visrealm/pico9918/img/digital_av.jpg

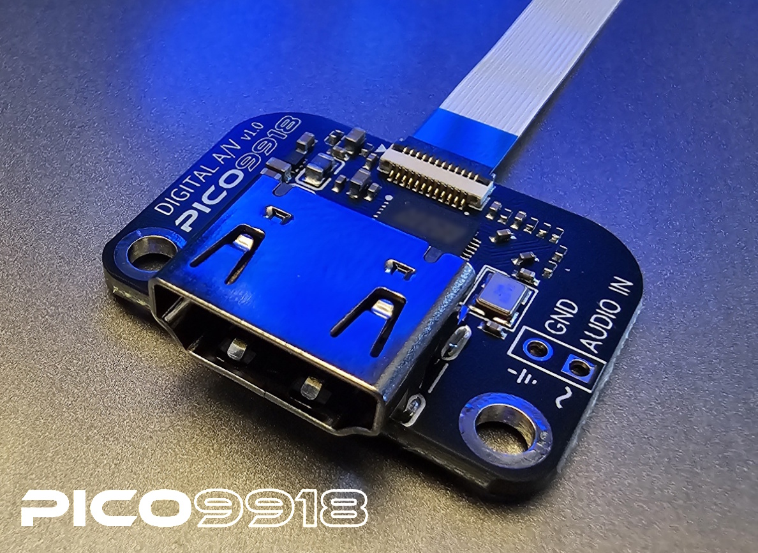
img/digital_av.jpg
