visrealm/pico9918/img/nocut-ffc.jpg

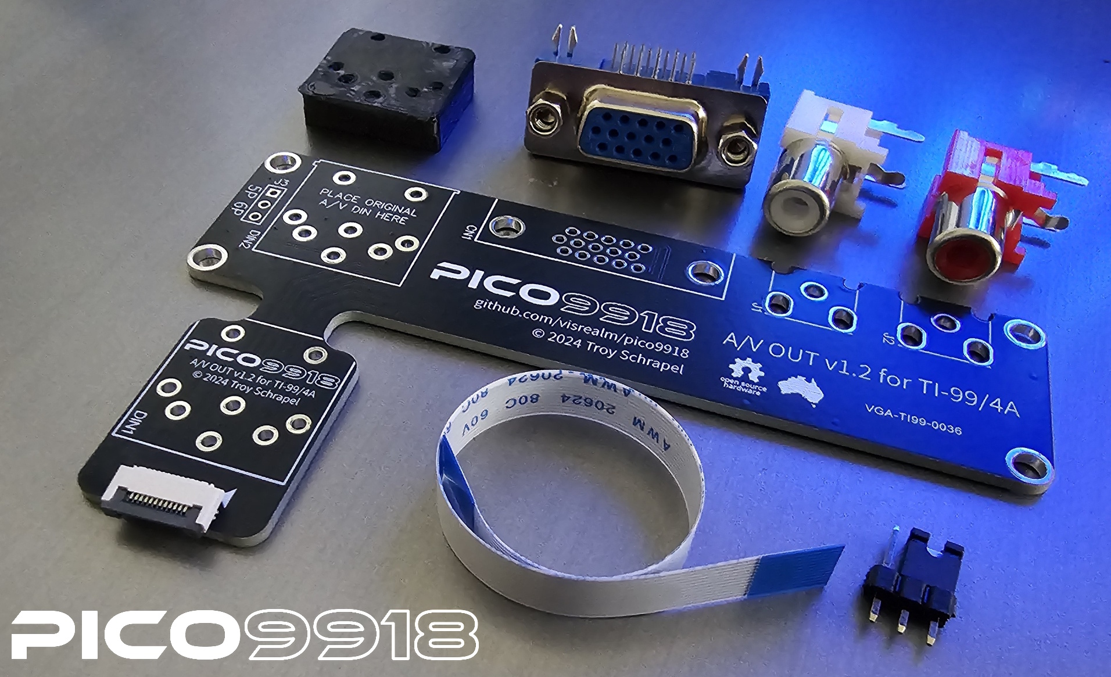
img/nocut-ffc.jpg
