visrealm/pico9918/img/pico9918_v0_3_sm2.jpg

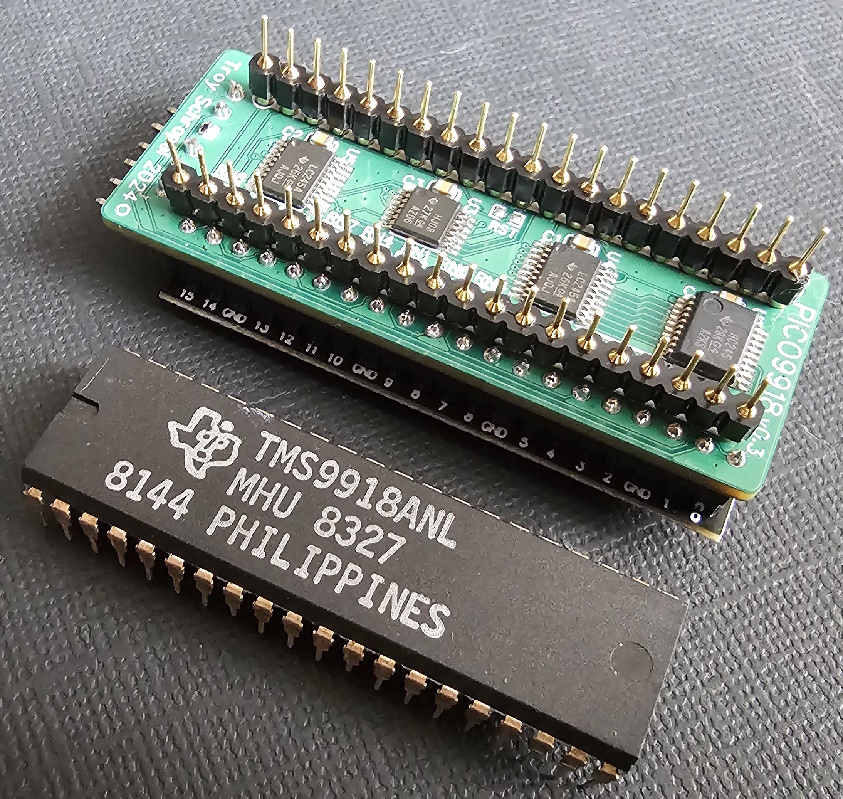
img/pico9918_v0_3_sm2.jpg
