visrealm/pico9918/nocut/ti99/img/nocut-ti99-enclosure-1.jpg

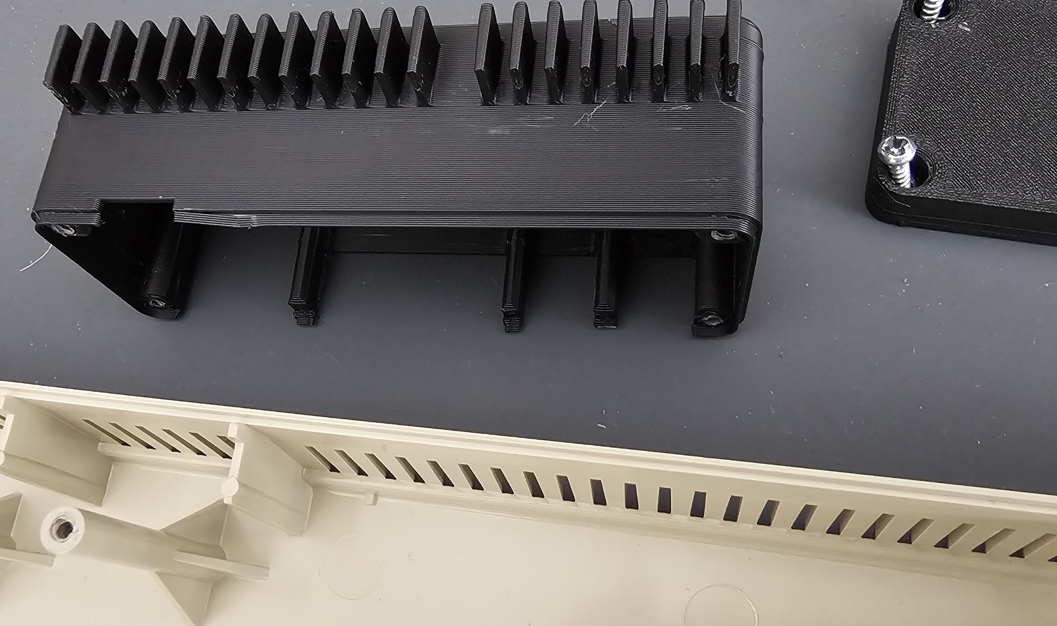
nocut/ti99/img/nocut-ti99-enclosure-1.jpg
