visrealm/pico9918/nocut/ti99/img/nocut-ti99-enclosure-3.jpg

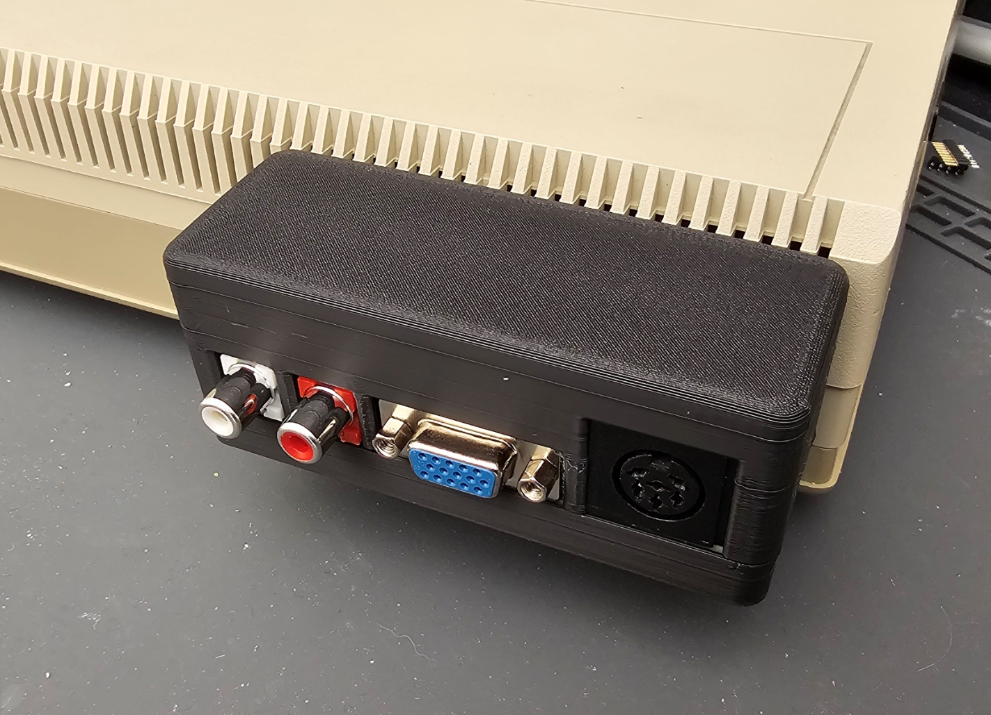
nocut/ti99/img/nocut-ti99-enclosure-3.jpg
